rallepalaveev/a2pico/A2Pico.v1.7/A2Pico.v1.7.sch.pdf

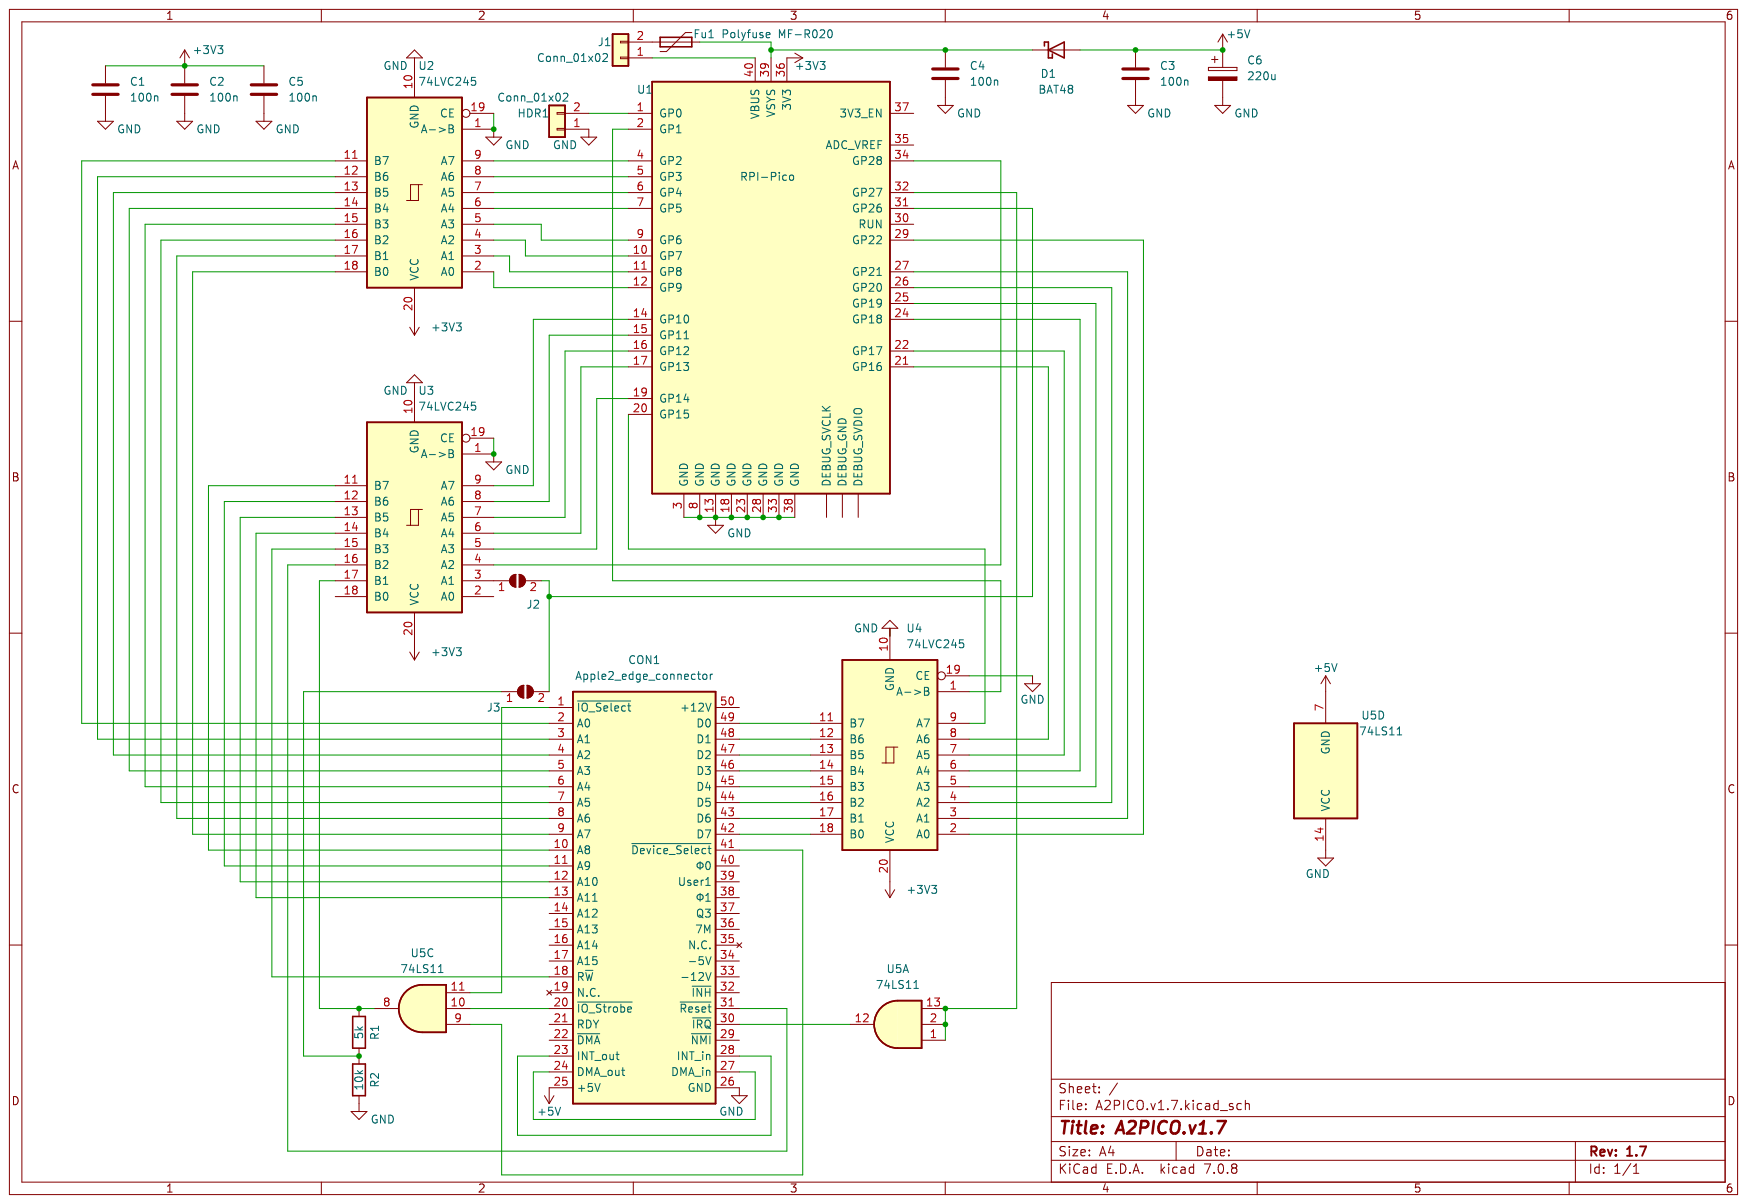
[picture p10: page 1]
