rallepalaveev/a2pico/A2Pico.v1.4/A2Pico.v1.4_sch.pdf

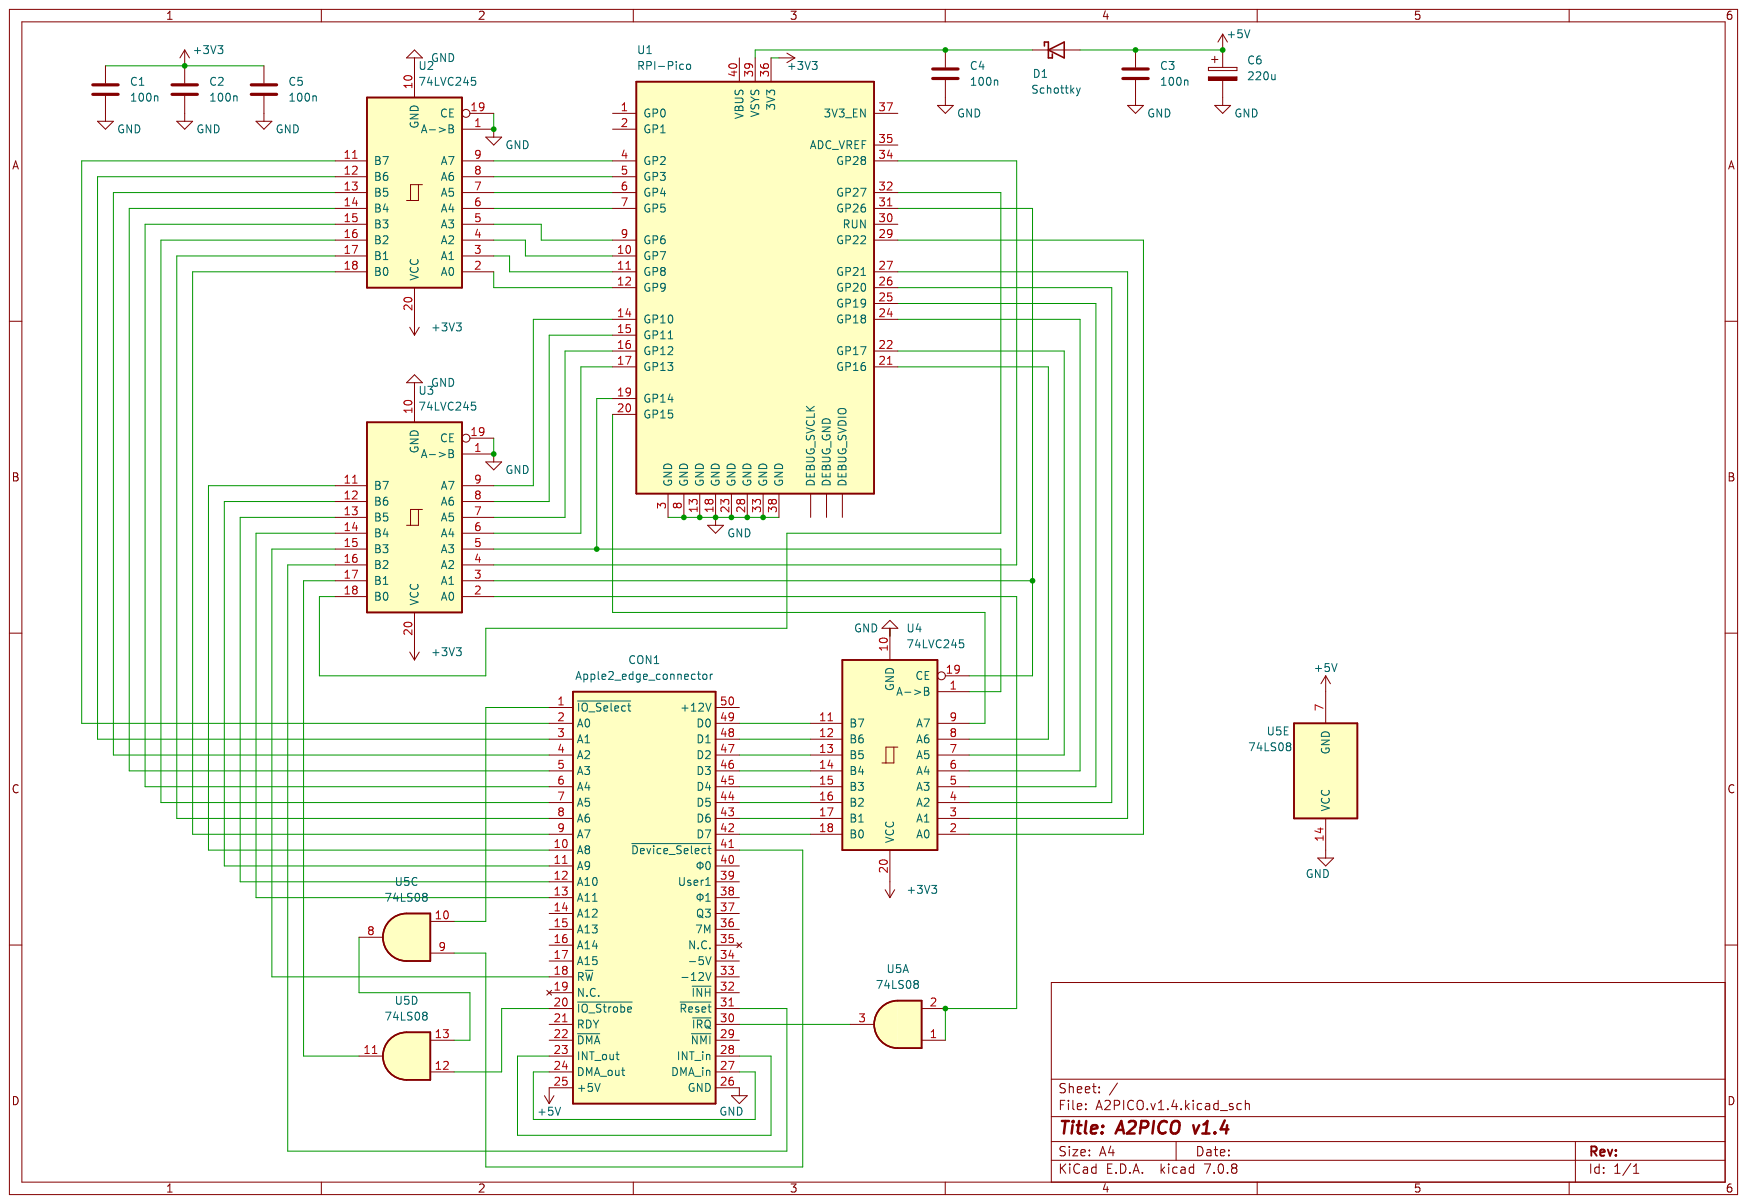
[picture p11: page 1]
